NijelB/Barkuspad/Early Pads/Barkuspad 1_1/Parts/Case/LID1_1.SLDPRT.STL

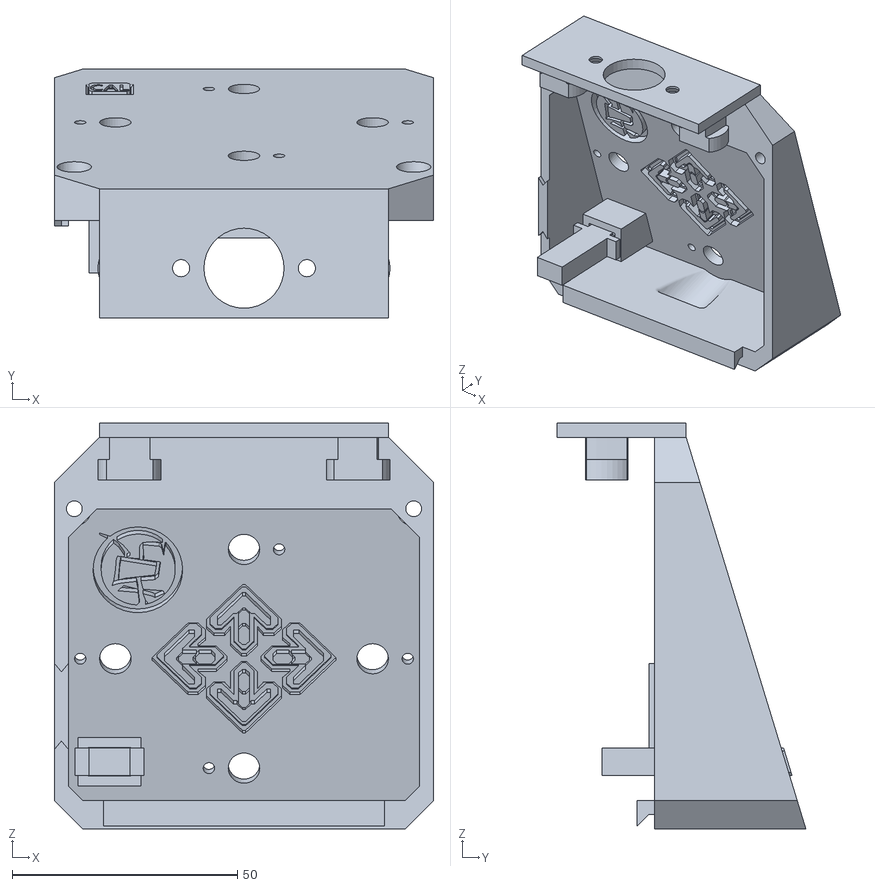
[picture p16: CAD file, 2024-05-16]
Early Pads/Barkuspad 1_1/Parts/Case/LID1_1.SLDPRT.STL
84.3 x 55.3 x 90.2
