NijelB/Barkuspad/Early Pads/Barkuspad 1_1/Parts/Control panel/Start select button base.stl

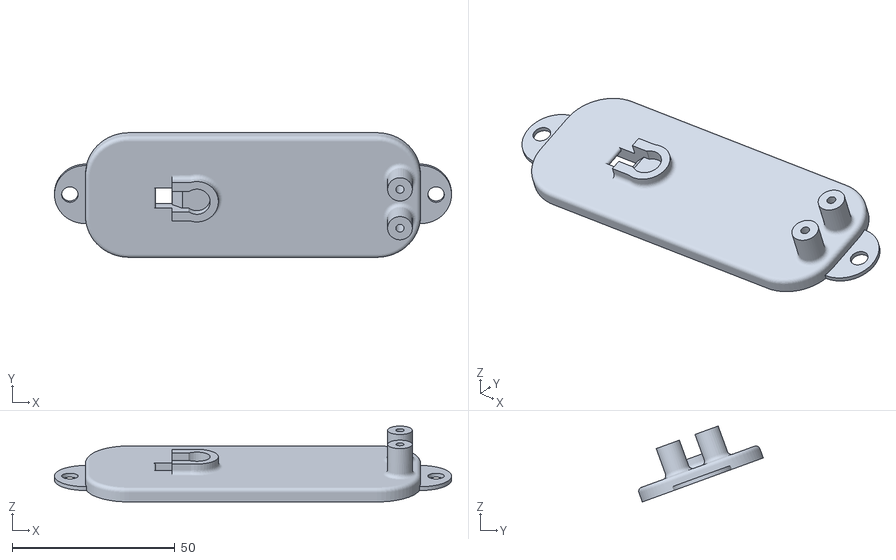
[picture p17: CAD file, 2024-05-16]
Early Pads/Barkuspad 1_1/Parts/Control panel/Start select button base.stl
122.1 x 38.3 x 23.4
