NijelB/Barkuspad/Early Pads/Barkuspad 1_1/Parts/PanelPieces/Contact.STL

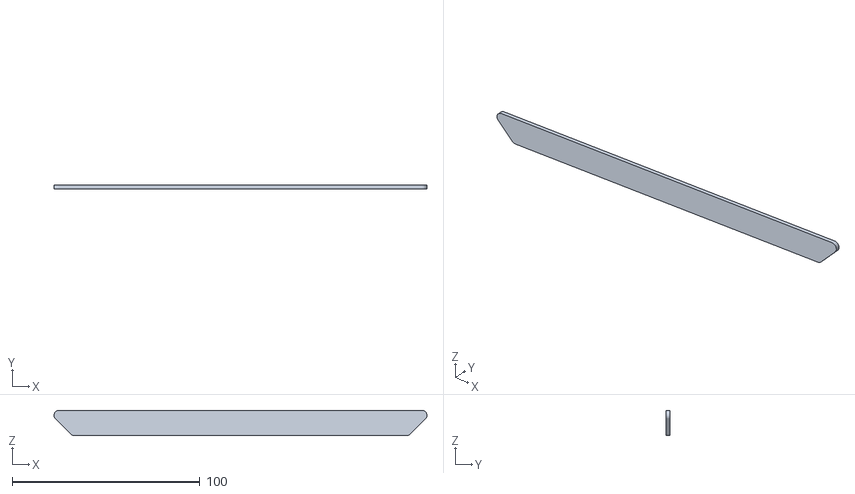
[picture p18: CAD file, 2024-05-16]
Early Pads/Barkuspad 1_1/Parts/PanelPieces/Contact.STL
198.8 x 2.03 x 13.3
