NijelB/Barkuspad/Early Pads/Barkuspad 1_1/Parts/Printing Files/Control Box Cover Ramped.stl

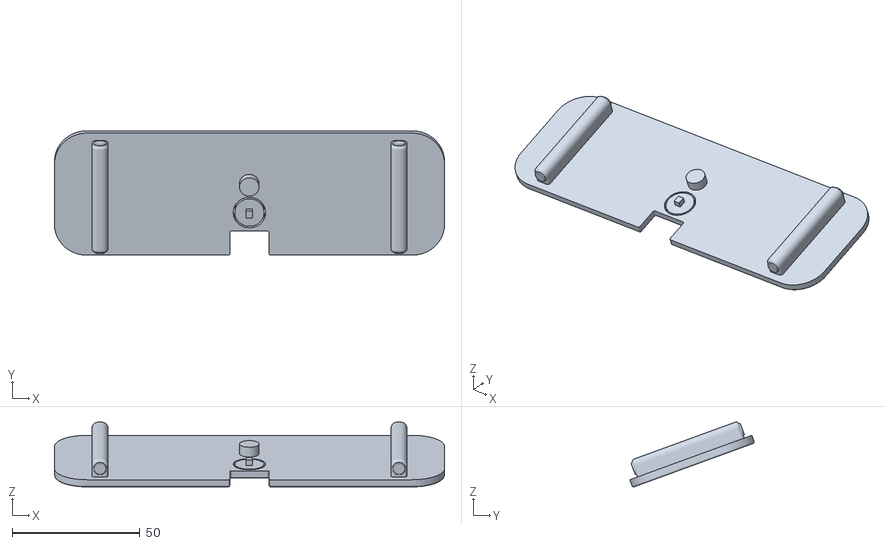
[picture p19: CAD file, 2024-05-16]
Early Pads/Barkuspad 1_1/Parts/Printing Files/Control Box Cover Ramped.stl
152.4 x 48.6 x 25.3
