NijelB/Barkuspad/Early Pads/Barkuspad 1_2/Parts/Corner_bracket.stl

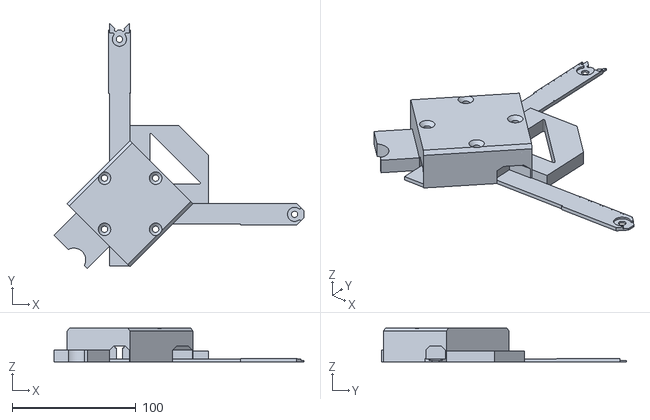
[picture p20: CAD file, 2024-05-16]
Early Pads/Barkuspad 1_2/Parts/Corner_bracket.stl
201.8 x 197.7 x 27.3
