NijelB/Barkuspad/Early Pads/Barkuspad 1_3/Parts/Button_base.stl

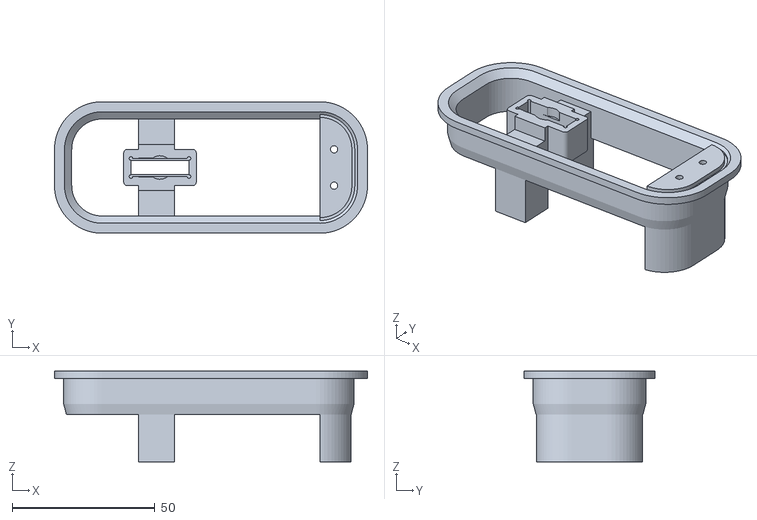
[picture p21: CAD file, 2024-05-16]
Early Pads/Barkuspad 1_3/Parts/Button_base.stl
109.5 x 46.0 x 31.8
