NijelB/Barkuspad/Early Pads/Barkuspad 1_3/Parts/Contacts/OuterBumper1.stl

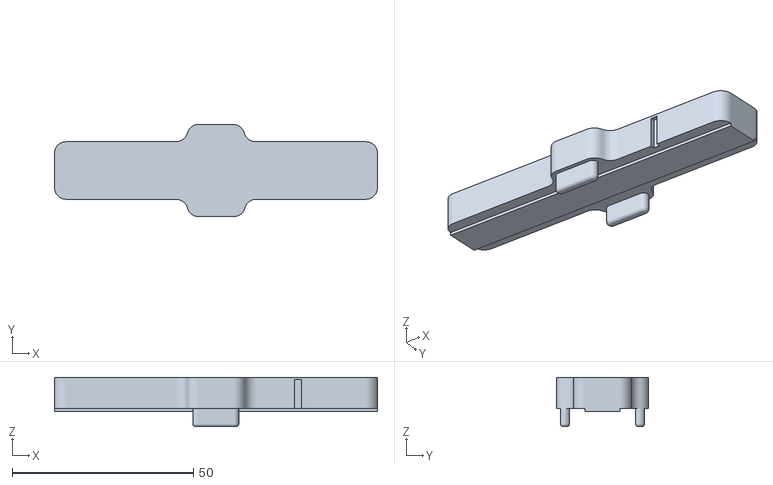
[picture p22: CAD file, 2024-05-16]
Early Pads/Barkuspad 1_3/Parts/Contacts/OuterBumper1.stl
89.0 x 25.4 x 13.6
