NijelB/Barkuspad/Early Pads/Barkuspad 1_3/Parts/Contacts/V2 Bumpers/OuterHard I.stl

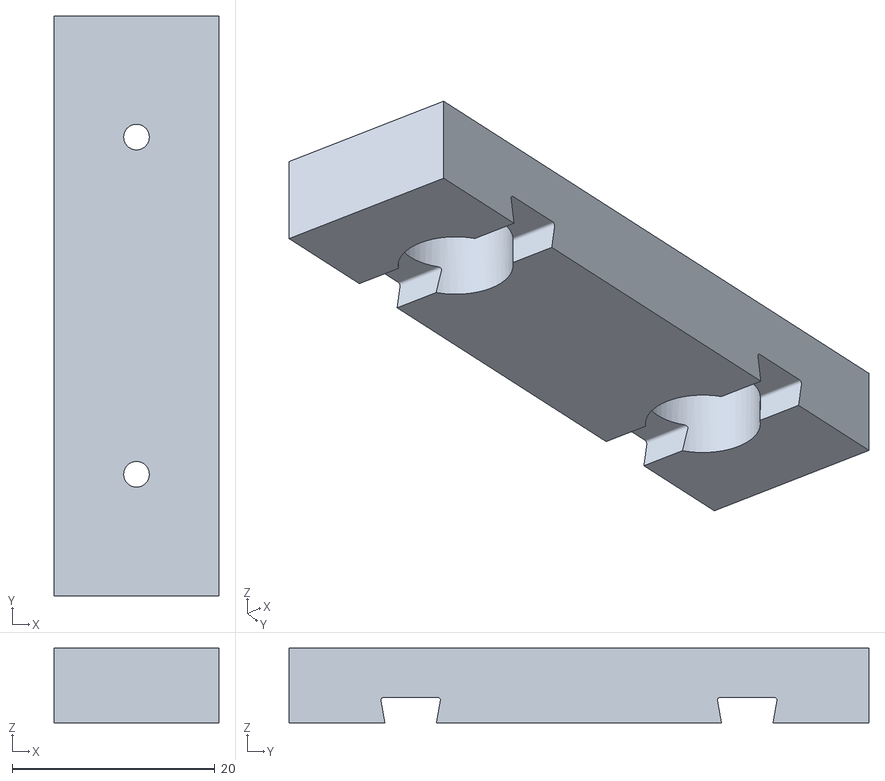
[picture p23: CAD file, 2024-05-16]
Early Pads/Barkuspad 1_3/Parts/Contacts/V2 Bumpers/OuterHard I.stl
16.3 x 57.2 x 7.37
