NijelB/Barkuspad/Barkuspad 1_4/Parts/Contacts/Inner_contact_base.stl

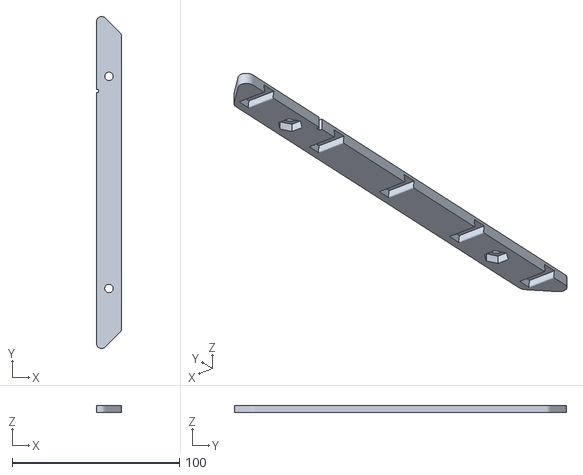
[picture p24: CAD file, 2024-05-16]
Barkuspad 1_4/Parts/Contacts/Inner_contact_base.stl
15.2 x 198.8 x 4.45
