NijelB/Barkuspad/Barkuspad 1_4/Parts/CornerPiece.stl

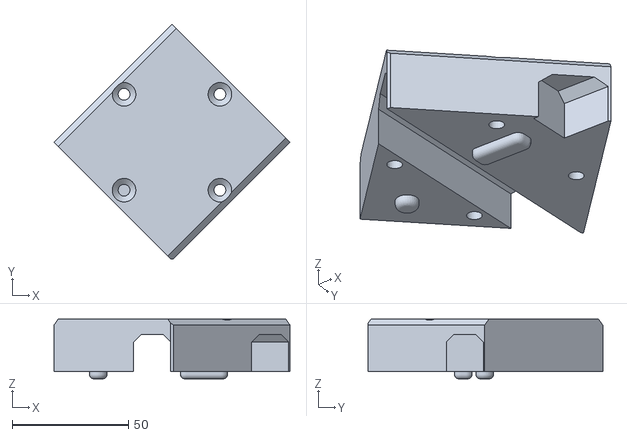
[picture p25: CAD file, 2024-05-16]
Barkuspad 1_4/Parts/CornerPiece.stl
101.6 x 101.0 x 25.7
