NijelB/Barkuspad/Early Pads/Barkuspad 1_1/Parts/BodyPieces/Corner_Brace_6.STL

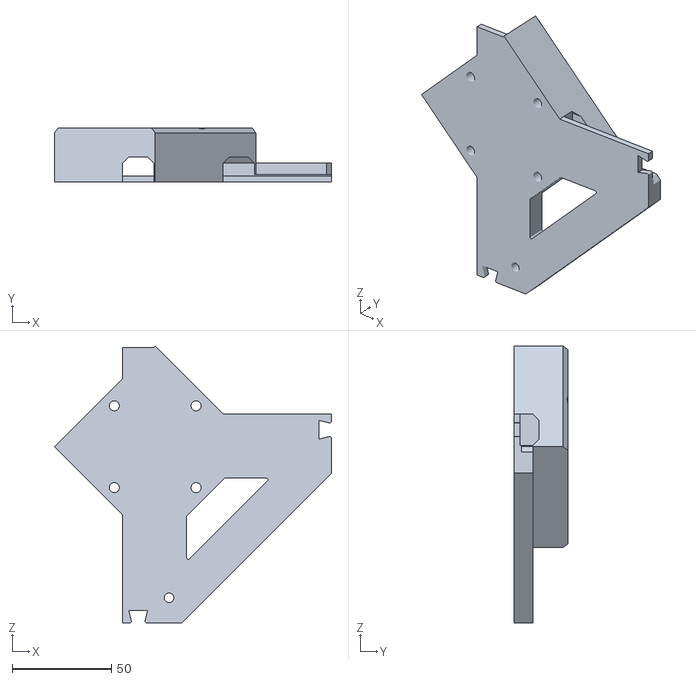
[picture p26: CAD file, 2024-05-16]
Early Pads/Barkuspad 1_1/Parts/BodyPieces/Corner_Brace_6.STL
139.7 x 27.3 x 139.7
