NijelB/Barkuspad/Early Pads/Barkuspad 1_1/Parts/Case/RST1_1.SLDPRT

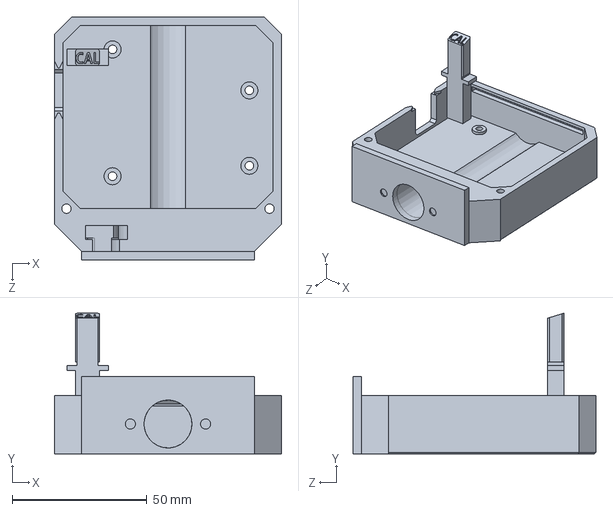
[picture p27: CAD file, 2024-05-16]
Early Pads/Barkuspad 1_1/Parts/Case/RST1_1.SLDPRT
84.3 x 52.2 x 90.2 mm
