NijelB/Barkuspad/Early Pads/Barkuspad 1_1/Parts/Printing Files/Corner brace cap~.stl

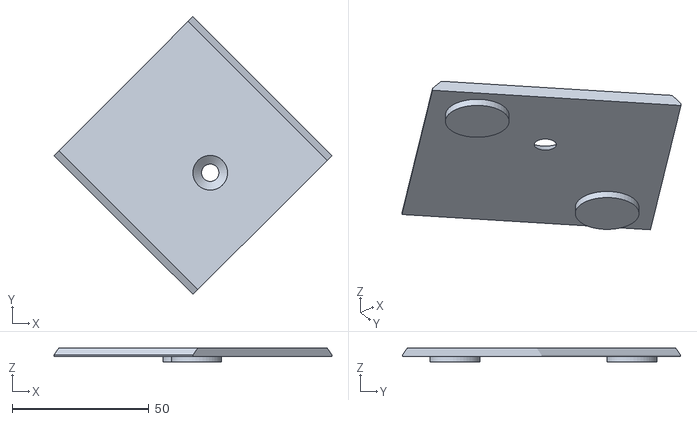
[picture p28: CAD file, 2024-05-16]
Early Pads/Barkuspad 1_1/Parts/Printing Files/Corner brace cap~.stl
101.6 x 101.6 x 5.21
