NijelB/Barkuspad/Early Pads/Barkuspad 1_3/Parts/Contacts/OuterBumper3.stl

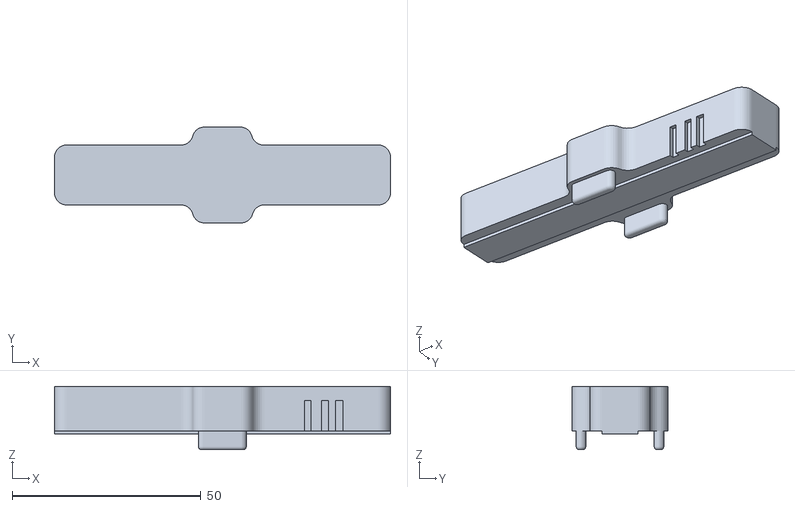
[picture p30: CAD file, 2024-05-16]
Early Pads/Barkuspad 1_3/Parts/Contacts/OuterBumper3.stl
89.0 x 25.4 x 16.8
