NijelB/Barkuspad/Early Pads/Barkuspad 1_3/Parts/Contacts/V2 Bumpers/OuterSoft I.stl

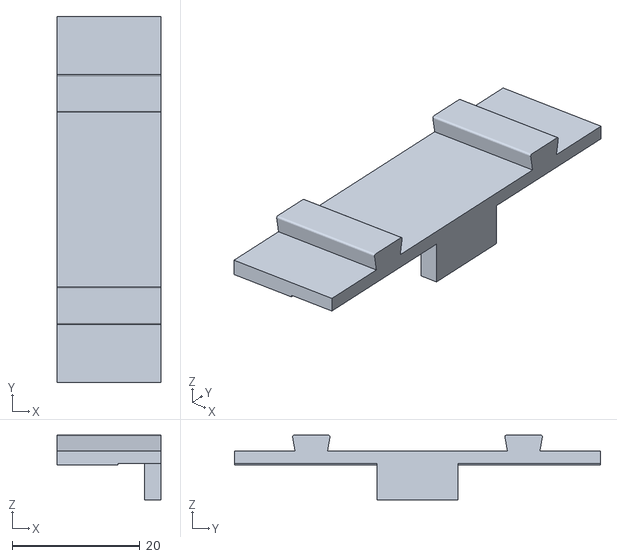
[picture p31: CAD file, 2024-05-16]
Early Pads/Barkuspad 1_3/Parts/Contacts/V2 Bumpers/OuterSoft I.stl
16.3 x 57.2 x 10.1
