NijelB/Barkuspad/Early Pads/Barkuspad 1_3/Parts/Corner_ piece.stl

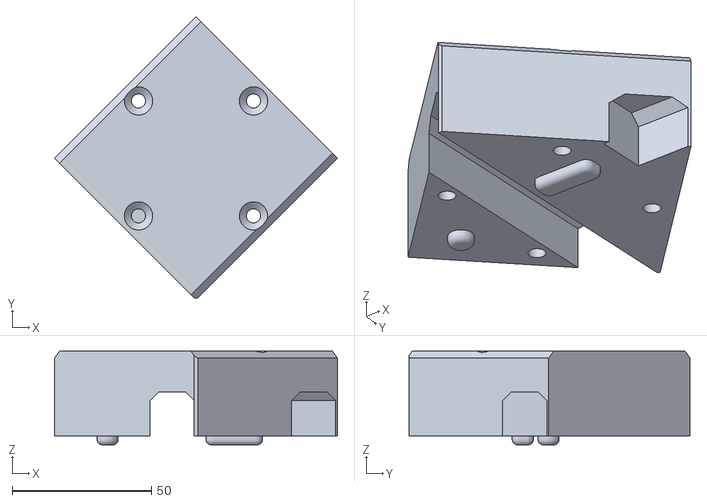
[picture p32: CAD file, 2024-05-16]
Early Pads/Barkuspad 1_3/Parts/Corner_ piece.stl
101.6 x 101.0 x 33.7
