NijelB/Barkuspad/Barkuspad 1_4/Parts/Contacts/Inner_contact_tpu_tall.stl

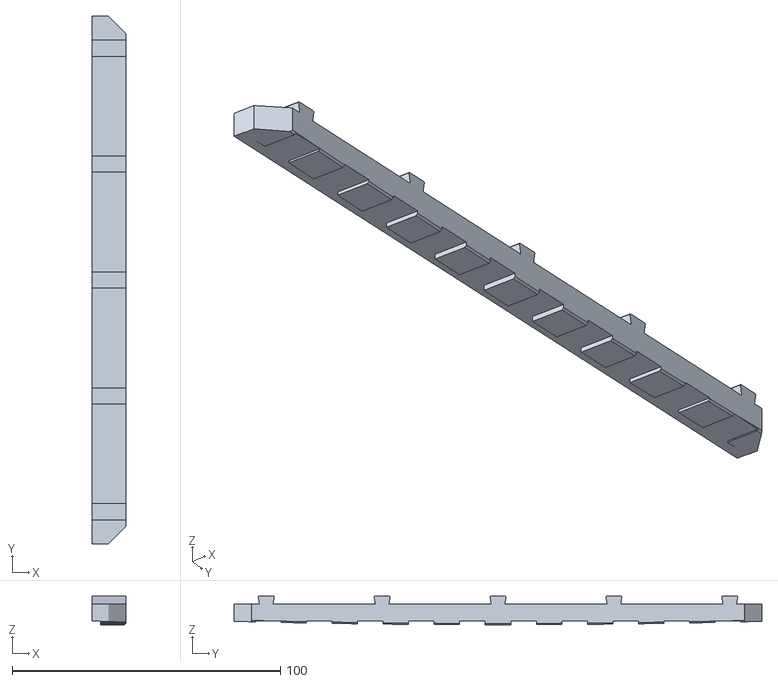
[picture p33: CAD file, 2024-05-16]
Barkuspad 1_4/Parts/Contacts/Inner_contact_tpu_tall.stl
12.7 x 196.9 x 10.7
