NijelB/Barkuspad/Barkuspad 1_4/Parts/knob.stl

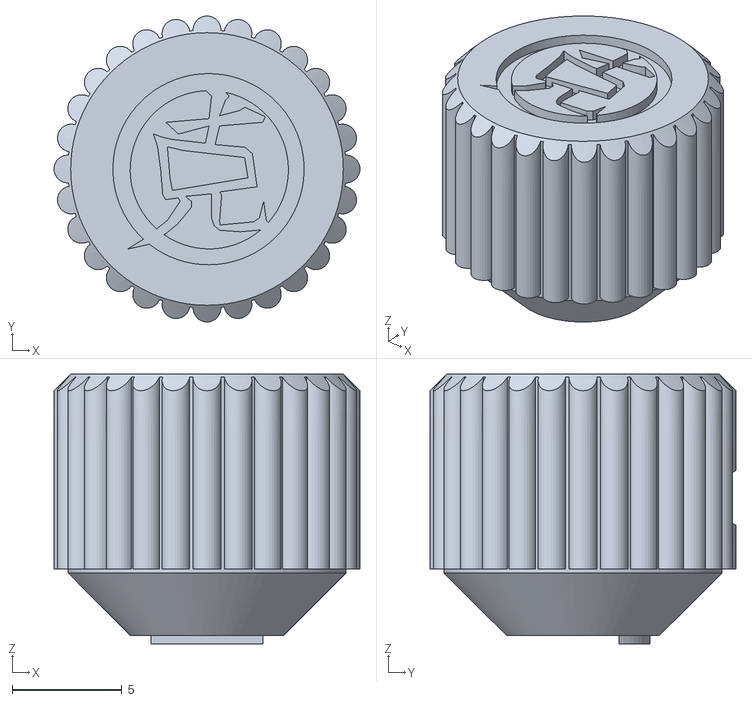
[picture p34: CAD file, 2024-05-16]
Barkuspad 1_4/Parts/knob.stl
14.0 x 14.0 x 12.3
