NijelB/Barkuspad/Early Pads/Barkuspad 1_1/Parts/BodyPieces/Corner_Brace_5.STL

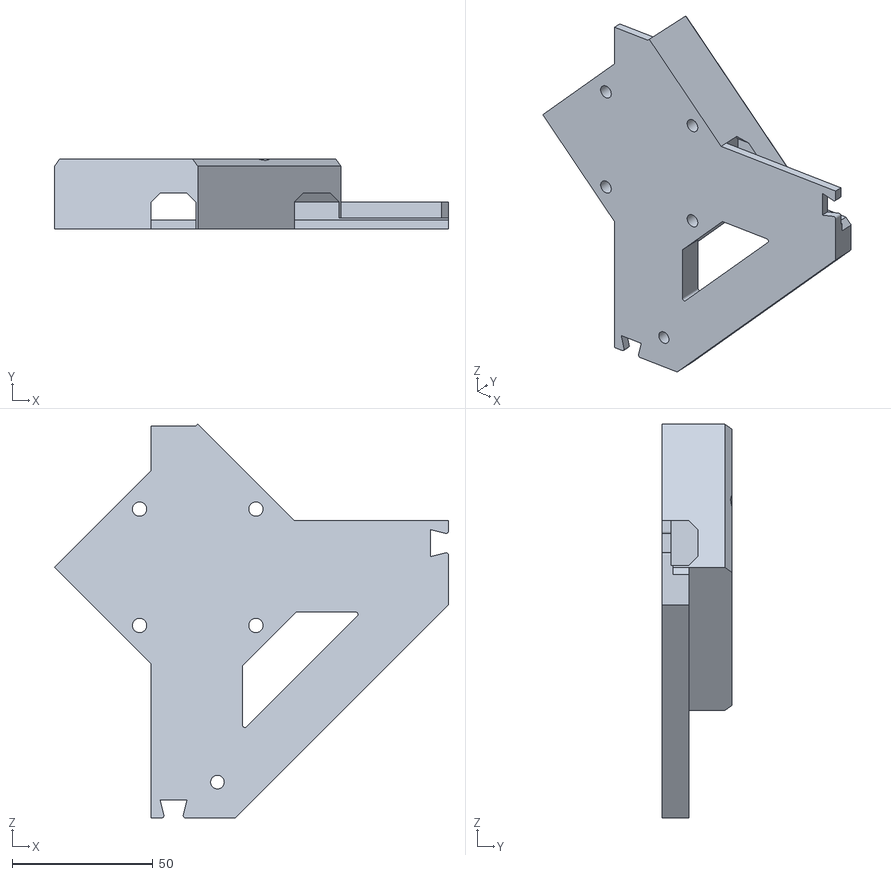
[picture p35: CAD file, 2024-05-16]
Early Pads/Barkuspad 1_1/Parts/BodyPieces/Corner_Brace_5.STL
139.7 x 24.8 x 139.7
