NijelB/Barkuspad/Early Pads/Barkuspad 1_1/Parts/Case/BASE1_2.STL

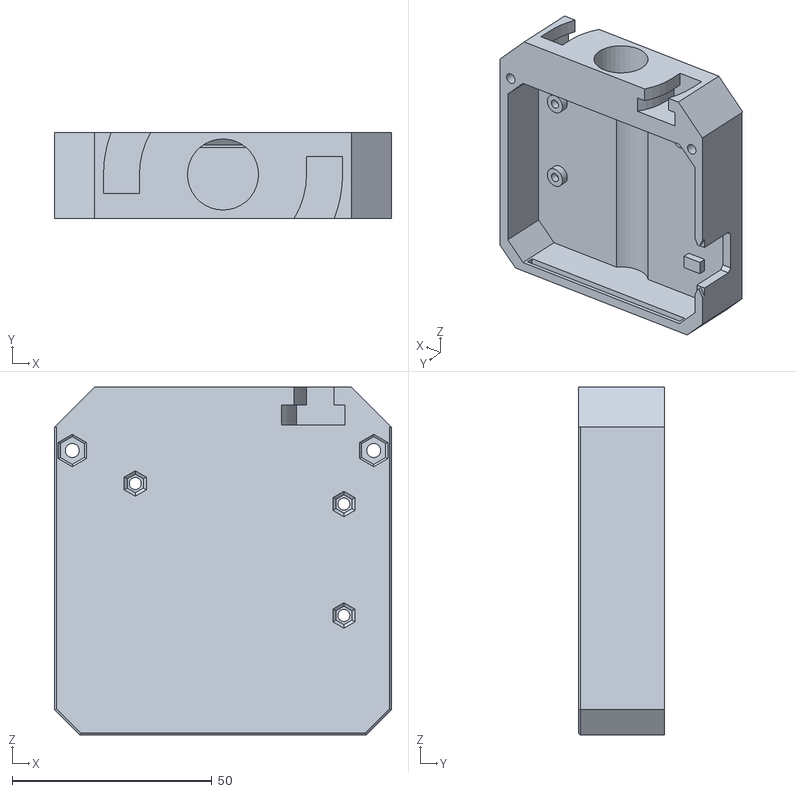
[picture p36: CAD file, 2024-05-16]
Early Pads/Barkuspad 1_1/Parts/Case/BASE1_2.STL
84.3 x 21.6 x 87.0
