NijelB/Barkuspad/Early Pads/Barkuspad 1_2/Parts/Spacer.stl

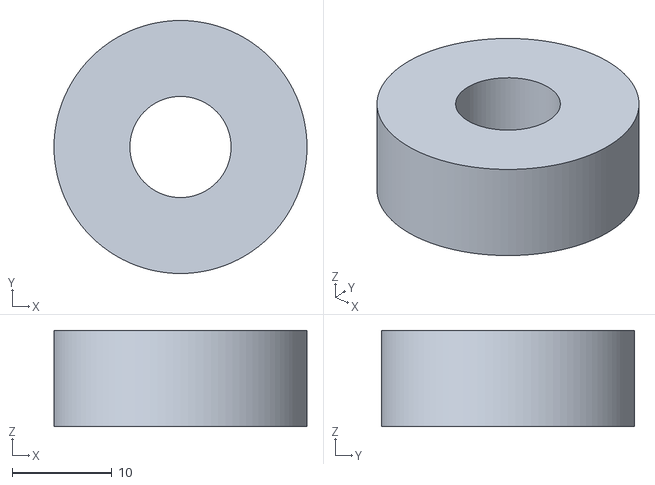
[picture p37: CAD file, 2024-05-16]
Early Pads/Barkuspad 1_2/Parts/Spacer.stl
25.4 x 25.4 x 9.65
