NijelB/Barkuspad/Early Pads/Barkuspad 1_3/Parts/Contacts/InnerBumper3.stl

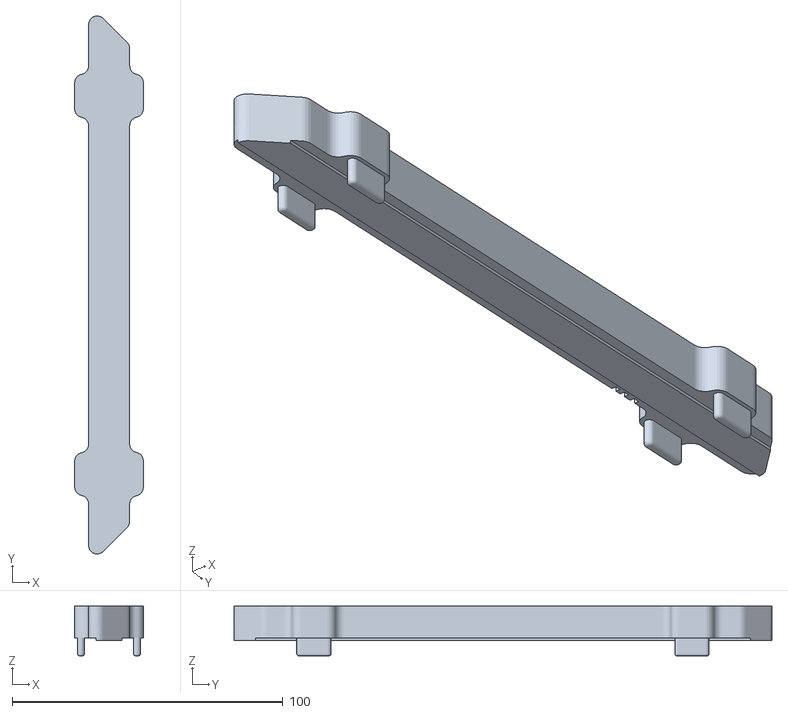
[picture p38: CAD file, 2024-05-16]
Early Pads/Barkuspad 1_3/Parts/Contacts/InnerBumper3.stl
25.4 x 198.8 x 18.4
