NijelB/Barkuspad/Early Pads/Barkuspad 1_3/Parts/Contacts/V2 Bumpers/RubberSlipInner.stl

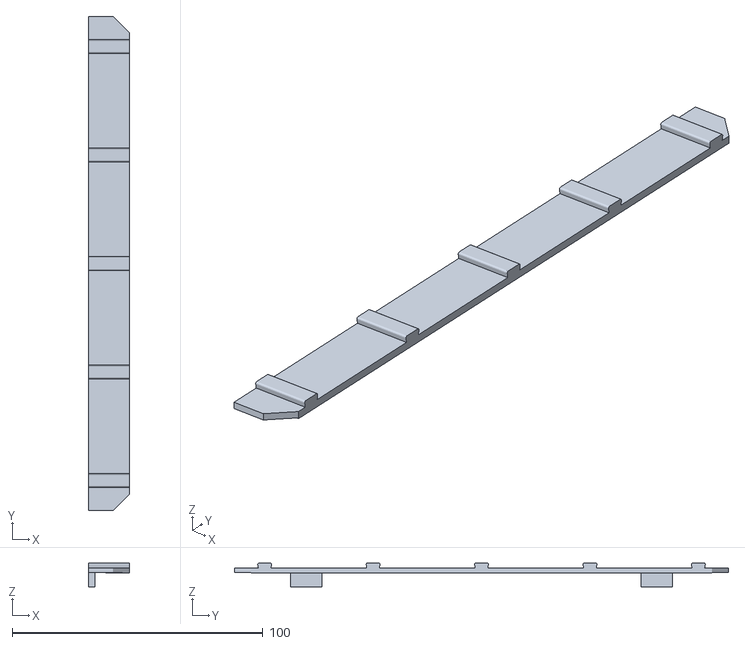
[picture p39: CAD file, 2024-05-16]
Early Pads/Barkuspad 1_3/Parts/Contacts/V2 Bumpers/RubberSlipInner.stl
16.4 x 196.9 x 9.54
