NijelB/Barkuspad/Early Pads/Barkuspad 1_3/Parts/Tile_Insert.stl

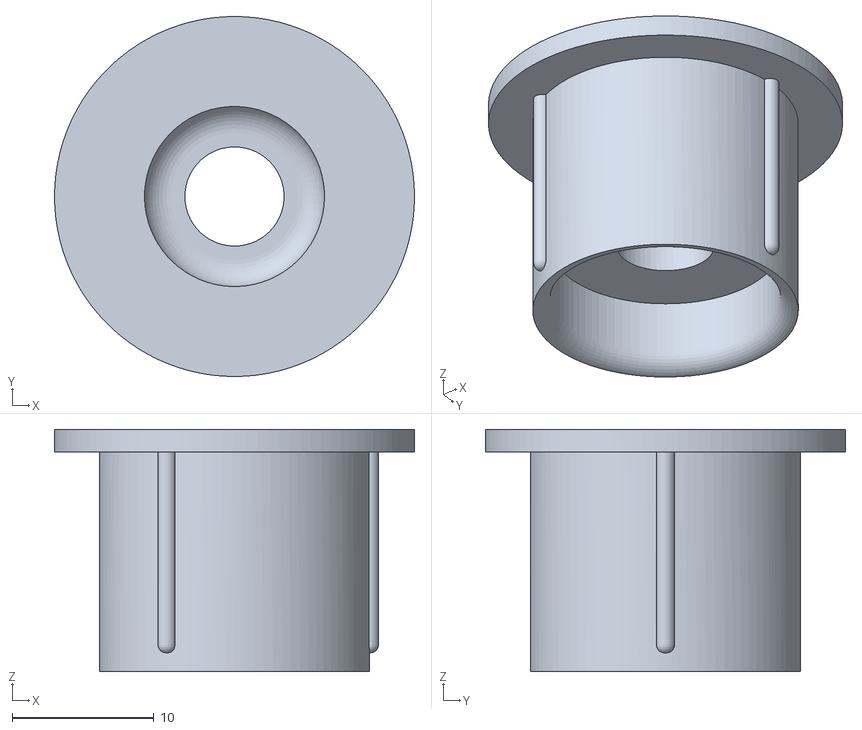
[picture p40: CAD file, 2024-05-16]
Early Pads/Barkuspad 1_3/Parts/Tile_Insert.stl
25.4 x 25.4 x 17.1
