NijelB/Barkuspad/Barkuspad 1_4/Parts/Tile_Base.stl

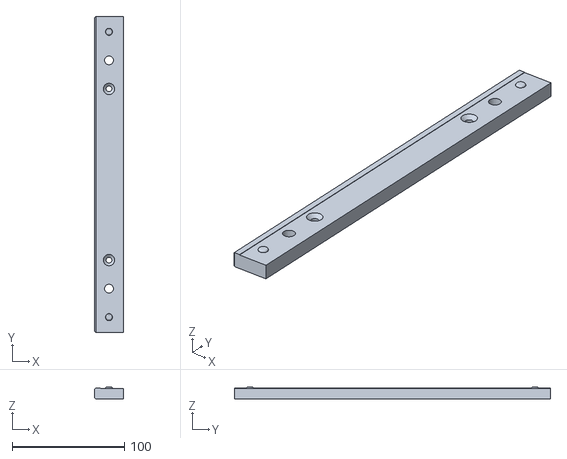
[picture p41: CAD file, 2024-05-16]
Barkuspad 1_4/Parts/Tile_Base.stl
25.4 x 281.3 x 10.8
