NijelB/Barkuspad/Early Pads/Barkuspad 1_1/Parts/Printing Files/TPUContact.stl

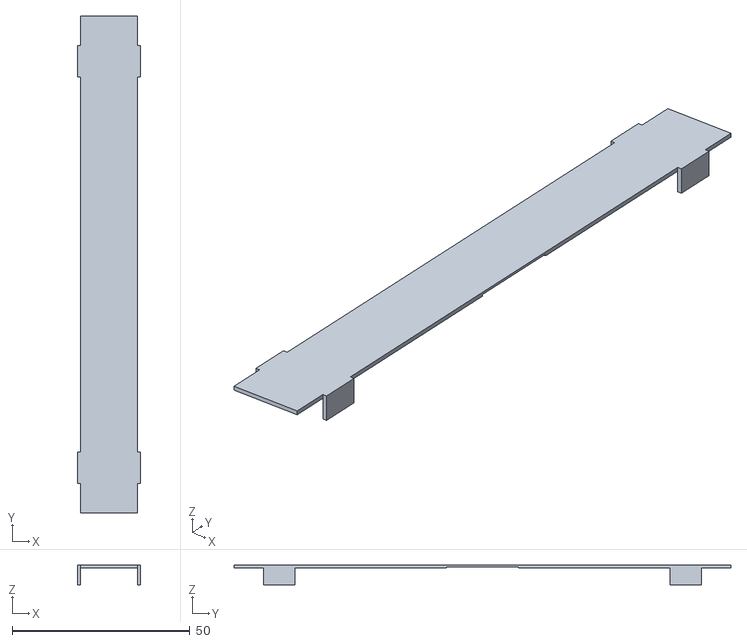
[picture p42: CAD file, 2024-05-16]
Early Pads/Barkuspad 1_1/Parts/Printing Files/TPUContact.stl
17.8 x 139.7 x 5.59
