NijelB/Barkuspad/Early Pads/Barkuspad 1_3/Parts/Button_button.stl

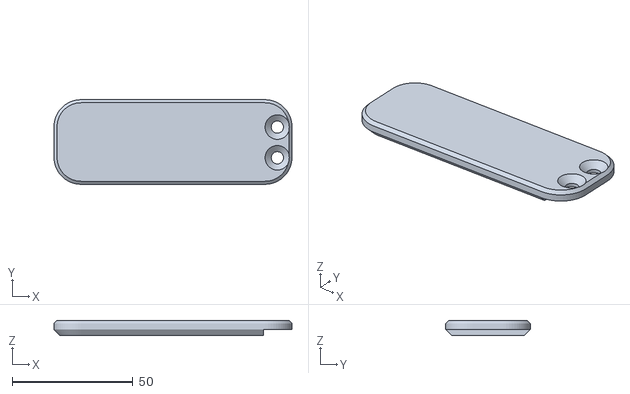
[picture p43: CAD file, 2024-05-16]
Early Pads/Barkuspad 1_3/Parts/Button_button.stl
98.6 x 35.1 x 6.35
