NijelB/Barkuspad/Barkuspad 1_4/Parts/CBoxTop.stl

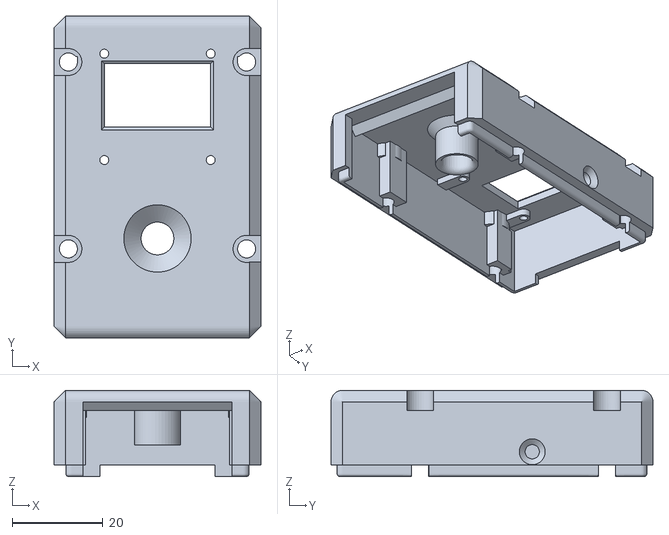
[picture p44: CAD file, 2024-05-16]
Barkuspad 1_4/Parts/CBoxTop.stl
45.7 x 71.1 x 19.0
