NijelB/Barkuspad/Early Pads/Barkuspad 1_1/Parts/BodyPieces/Cross_Brace_1.STL

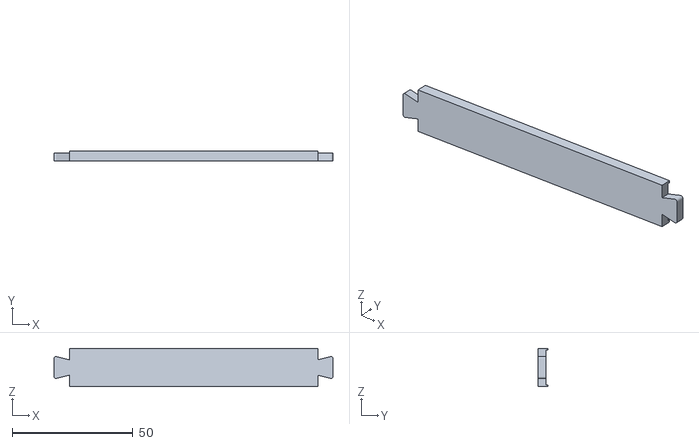
[picture p45: CAD file, 2024-05-16]
Early Pads/Barkuspad 1_1/Parts/BodyPieces/Cross_Brace_1.STL
115.5 x 3.94 x 15.9
