NijelB/Barkuspad/Early Pads/Barkuspad 1_1/Parts/Case/BASE2.STL

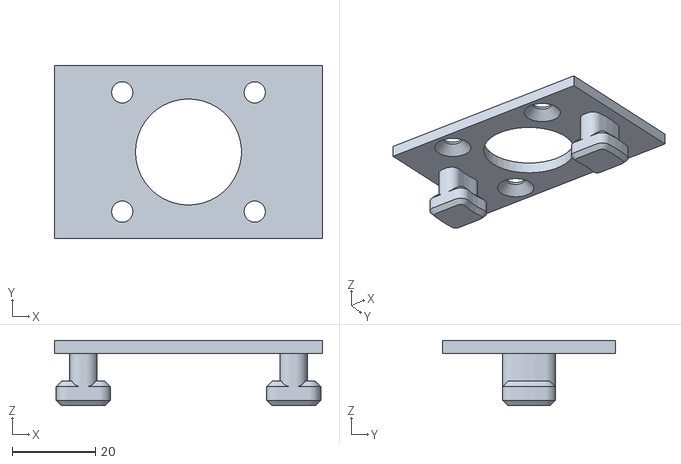
[picture p46: CAD file, 2024-05-16]
Early Pads/Barkuspad 1_1/Parts/Case/BASE2.STL
64.2 x 41.4 x 15.6
