NijelB/Barkuspad/Early Pads/Barkuspad 1_1/Parts/Printing Files/Panel bracket channeled.stl

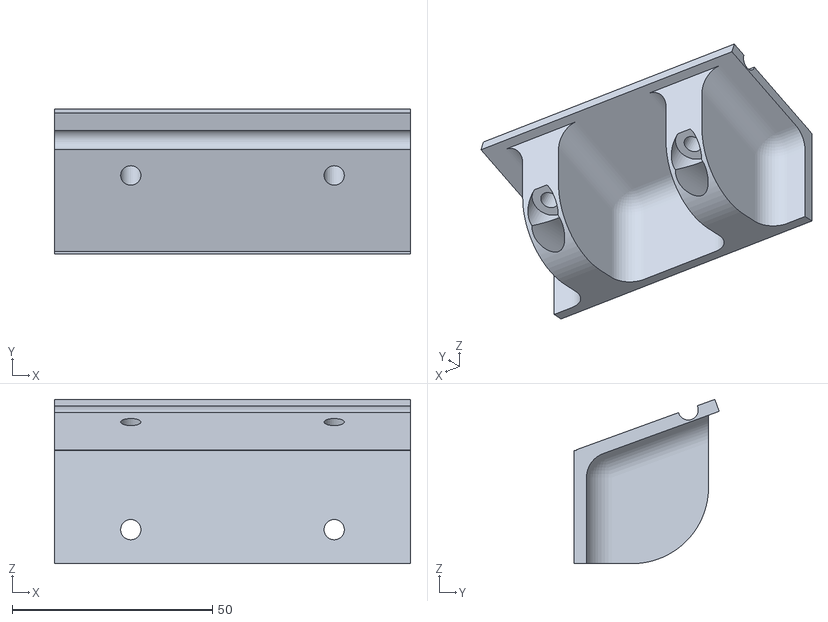
[picture p47: CAD file, 2024-05-16]
Early Pads/Barkuspad 1_1/Parts/Printing Files/Panel bracket channeled.stl
88.9 x 36.3 x 41.0
