NijelB/Barkuspad/Early Pads/Barkuspad 1_2/Parts/Inner_sensor_contact.stl

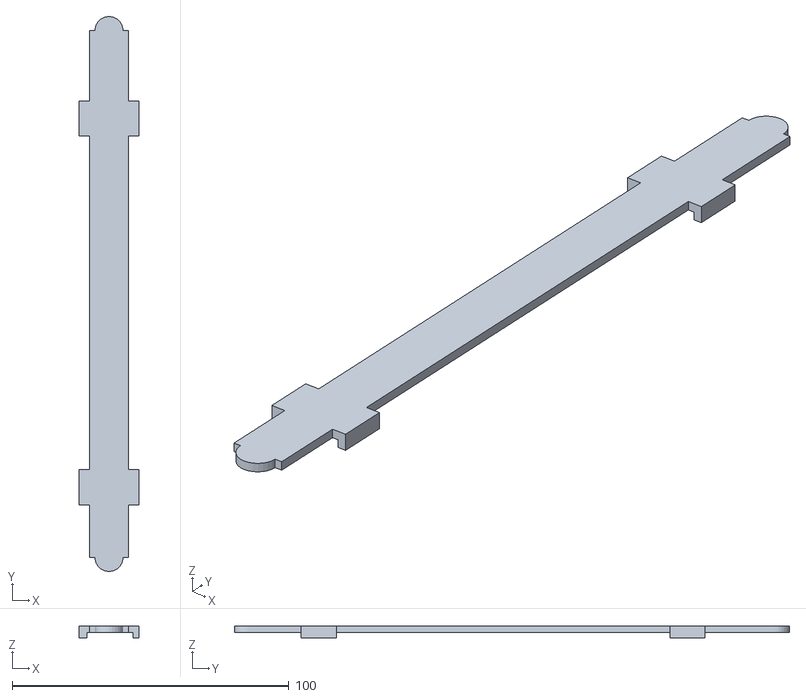
[picture p48: CAD file, 2024-05-16]
Early Pads/Barkuspad 1_2/Parts/Inner_sensor_contact.stl
21.6 x 200.7 x 4.29
