NijelB/Barkuspad/Barkuspad 1_4/Parts/CBoxBot.stl

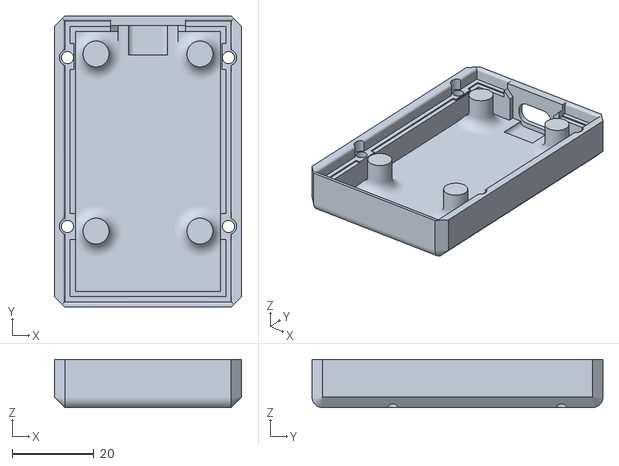
[picture p49: CAD file, 2024-05-16]
Barkuspad 1_4/Parts/CBoxBot.stl
45.7 x 71.1 x 11.7
