NijelB/Barkuspad/Early Pads/Barkuspad 1_1/Parts/BodyPieces/Corner_Brace_2.STL

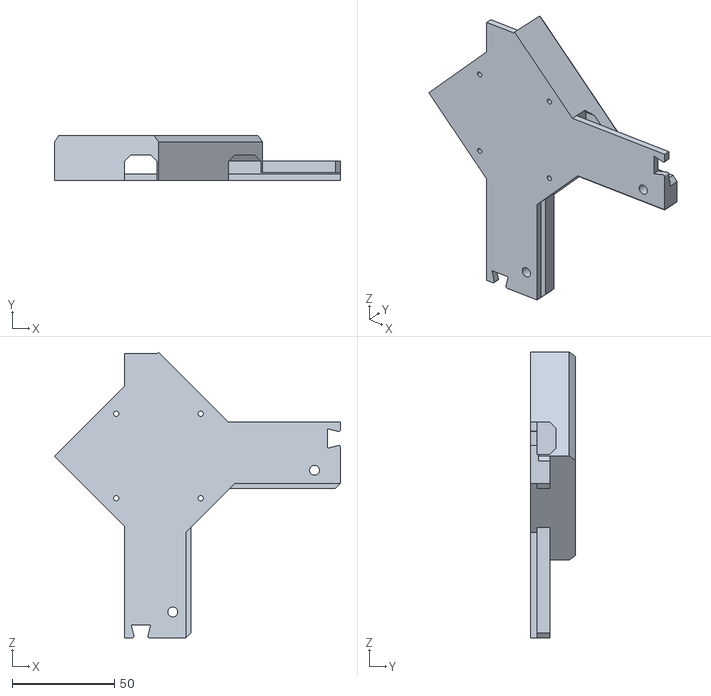
[picture p50: CAD file, 2024-05-16]
Early Pads/Barkuspad 1_1/Parts/BodyPieces/Corner_Brace_2.STL
139.7 x 22.2 x 139.7
