NijelB/Barkuspad/Early Pads/Barkuspad 1_1/Parts/Printing Files/New button.stl

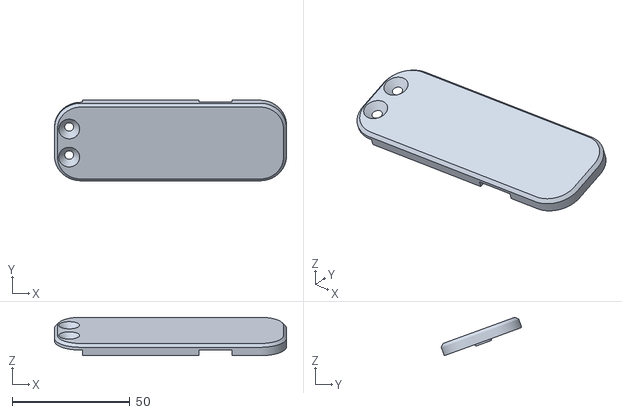
[picture p51: CAD file, 2024-05-16]
Early Pads/Barkuspad 1_1/Parts/Printing Files/New button.stl
98.6 x 34.2 x 16.3
