NijelB/Barkuspad/Early Pads/Barkuspad 1_1/Parts/BodyPieces/Cross_Brace_2.STL

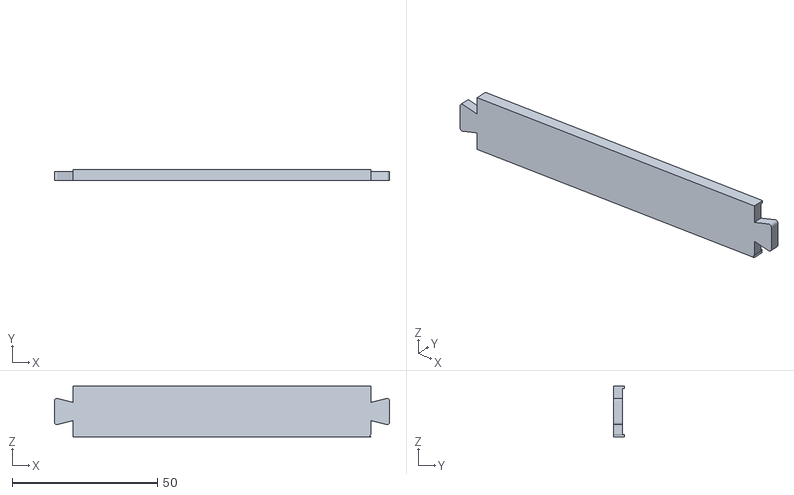
[picture p52: CAD file, 2024-05-16]
Early Pads/Barkuspad 1_1/Parts/BodyPieces/Cross_Brace_2.STL
115.5 x 3.96 x 17.5
