NijelB/Barkuspad/Early Pads/Barkuspad 1_1/Parts/Printing Files/Control Cluster Lipped.stl

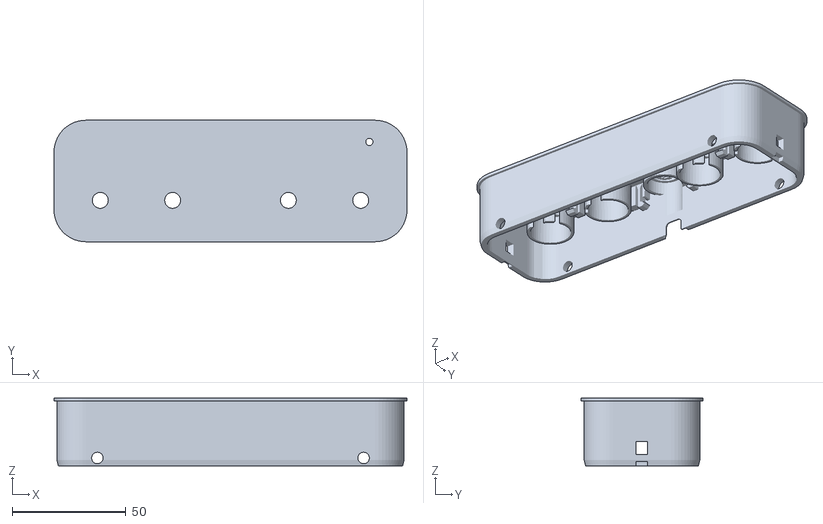
[picture p53: CAD file, 2024-05-16]
Early Pads/Barkuspad 1_1/Parts/Printing Files/Control Cluster Lipped.stl
154.9 x 53.3 x 29.8
