NijelB/Barkuspad/Early Pads/Barkuspad 1_2/Parts/Outer_track.stl

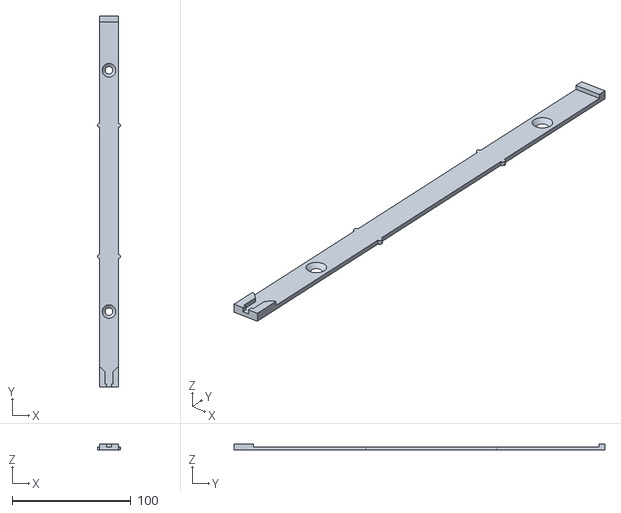
[picture p54: CAD file, 2024-05-16]
Early Pads/Barkuspad 1_2/Parts/Outer_track.stl
19.6 x 312.4 x 5.08
