NijelB/Barkuspad/Early Pads/Barkuspad 1_1/Parts/Printing Files/Corner brace V3 base.stl

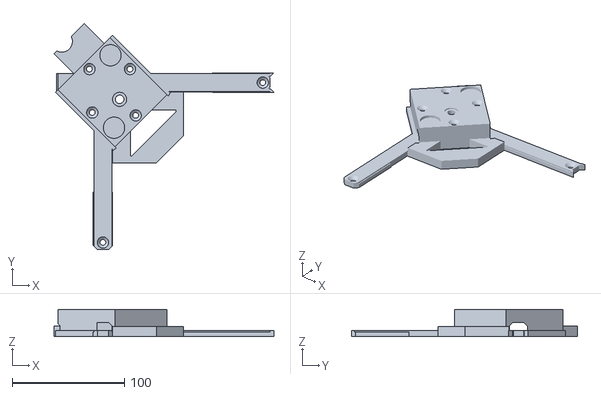
[picture p55: CAD file, 2024-05-16]
Early Pads/Barkuspad 1_1/Parts/Printing Files/Corner brace V3 base.stl
196.3 x 201.8 x 24.1
