NijelB/Barkuspad/Early Pads/Barkuspad 1_2/Parts/Outer_sensor_contact.stl

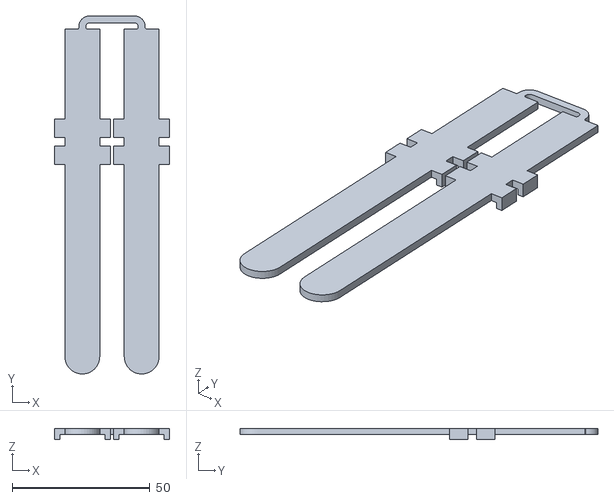
[picture p56: CAD file, 2024-05-16]
Early Pads/Barkuspad 1_2/Parts/Outer_sensor_contact.stl
41.9 x 130.2 x 4.17
