NijelB/Barkuspad/Early Pads/Barkuspad 1_1/Parts/Printing Files/New button base.stl

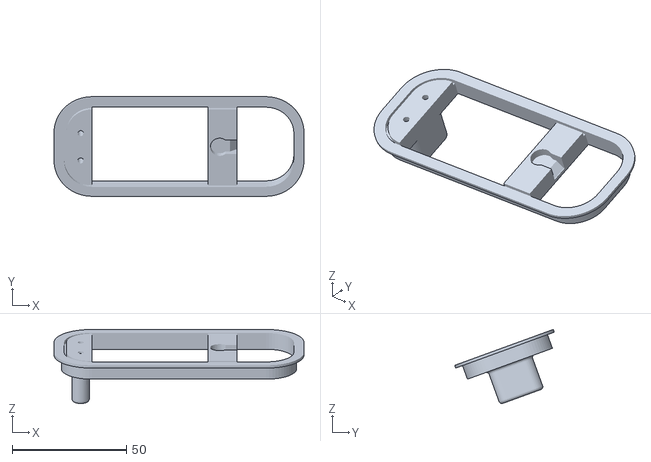
[picture p57: CAD file, 2024-05-16]
Early Pads/Barkuspad 1_1/Parts/Printing Files/New button base.stl
109.5 x 43.6 x 32.5
