NijelB/Barkuspad/Early Pads/Barkuspad 1_2/Parts/Panel_mount_center.stl

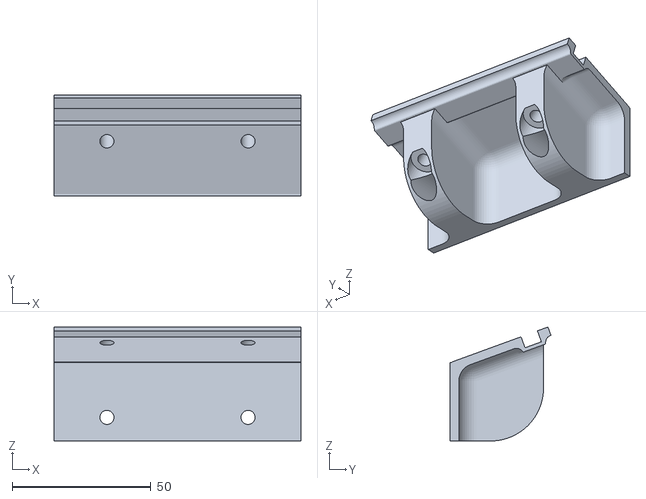
[picture p59: CAD file, 2024-05-16]
Early Pads/Barkuspad 1_2/Parts/Panel_mount_center.stl
88.9 x 36.3 x 41.0
